oscimp/wr_acorn/26_CERN_Workshop/figures/exp_locksweep_reboots.pdf

WR switch | m2sdr
| phase station

WR link

10 MHz out

auxclk 10 MHz

Microchip 53100A
