oscimp/wr_acorn/26_CERN_Workshop/figures/m2sdr_locksweep_fig.pdf

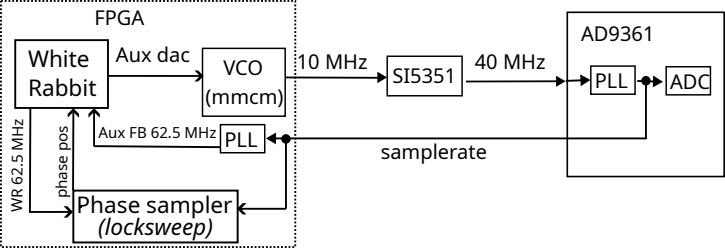
[picture p44: figure]
White Rabbit; Aux dac; VCO; FPGA; PLL; 10 MHz; 40 MHz; ADC; (mmcm); samplerate; Aux FB 62.5 MHz; Phase sampler (locksweep); WR 62.5 MHz; phase pos
