oscimp/wr_acorn/26_CERN_Workshop/figures/m2sdr_syntonized_fig.pdf

White Rabbit; 62.5 MHz; PLL; FPGA; 10 MHz; 40 MHz; ADC
