oscimp/wr_acorn/26_CERN_Workshop/figures/fig_wr_global_view.pdf

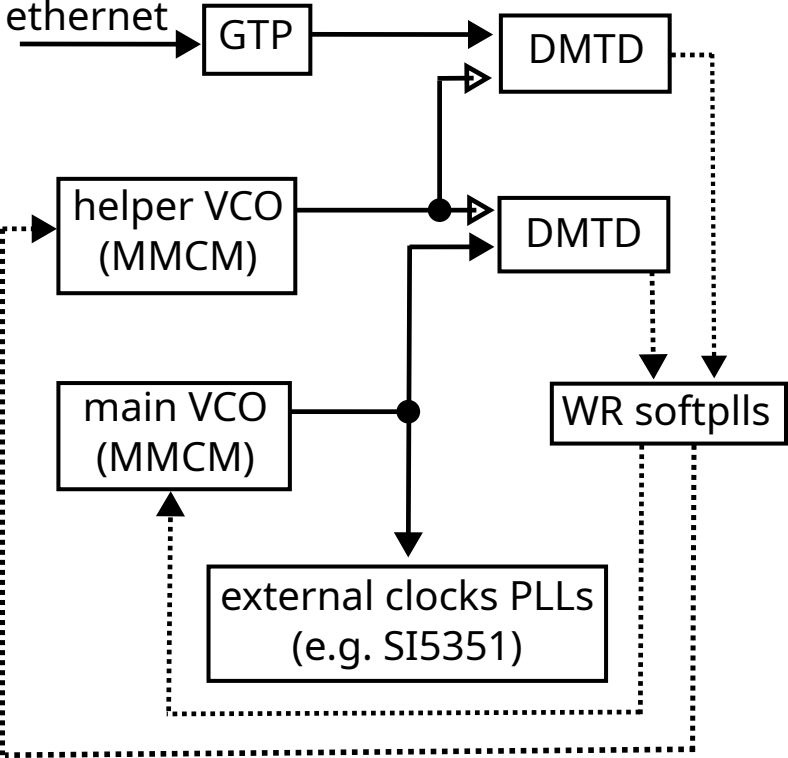
[picture p50: figure]
GTP; DMTD; main VCO (MMCM); helper VCO (MMCM); external clocks PLLs (e.g. SI5351); WR softplls; ethernet
