oscimp/wr_acorn/26_CERN_Workshop/figures/xcorr_principle.pdf

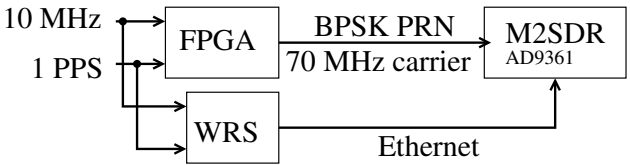
[picture p51: figure]
10 MHz; 1 PPS; FPGA; WRS; Ethernet; BPSK PRN; 70 MHz carrier; M2SDR
