oscimp/wr_acorn/26_CERN_Workshop/figures/ddmtd_schem.pdf

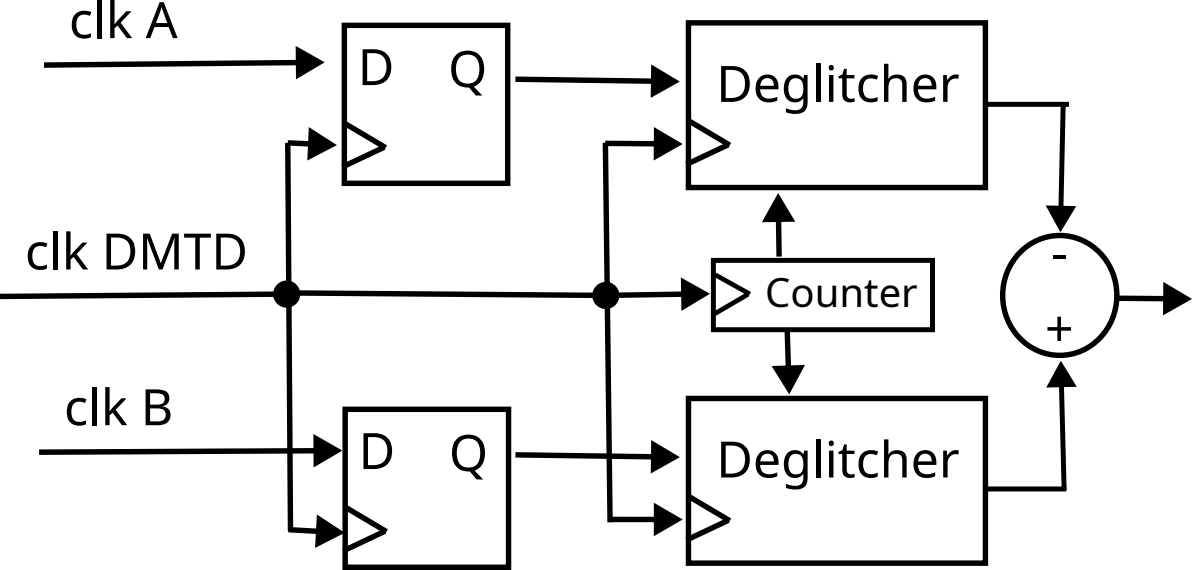
[picture p52: figure]
clk A; clk B; clk DMTD; Deglitcher; - Counter

φ
