oscimp/wr_acorn/26_CERN_Workshop/figures/exp_dmtd_noise_by_beat_freq.pdf

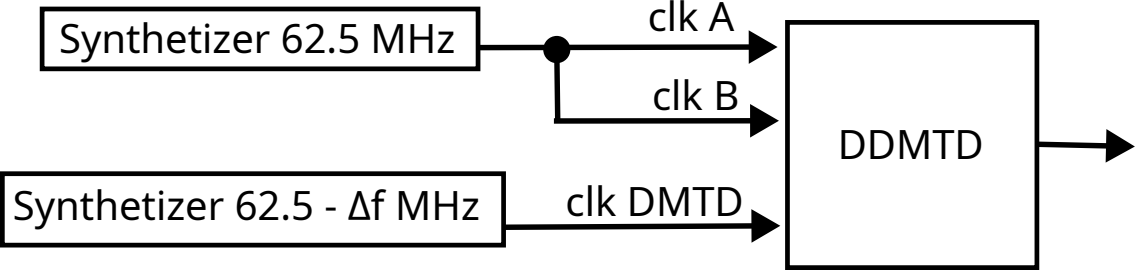
[picture p53: figure]
Synthetizer 62.5 MHz; Synthetizer 62.5 -; Δf MHz; DDMTD; clk A clk B; clk DMTD

P Welch
