oscimp/wr_acorn/26_CERN_Workshop/figures/exp_pll_lock_possibilities.pdf

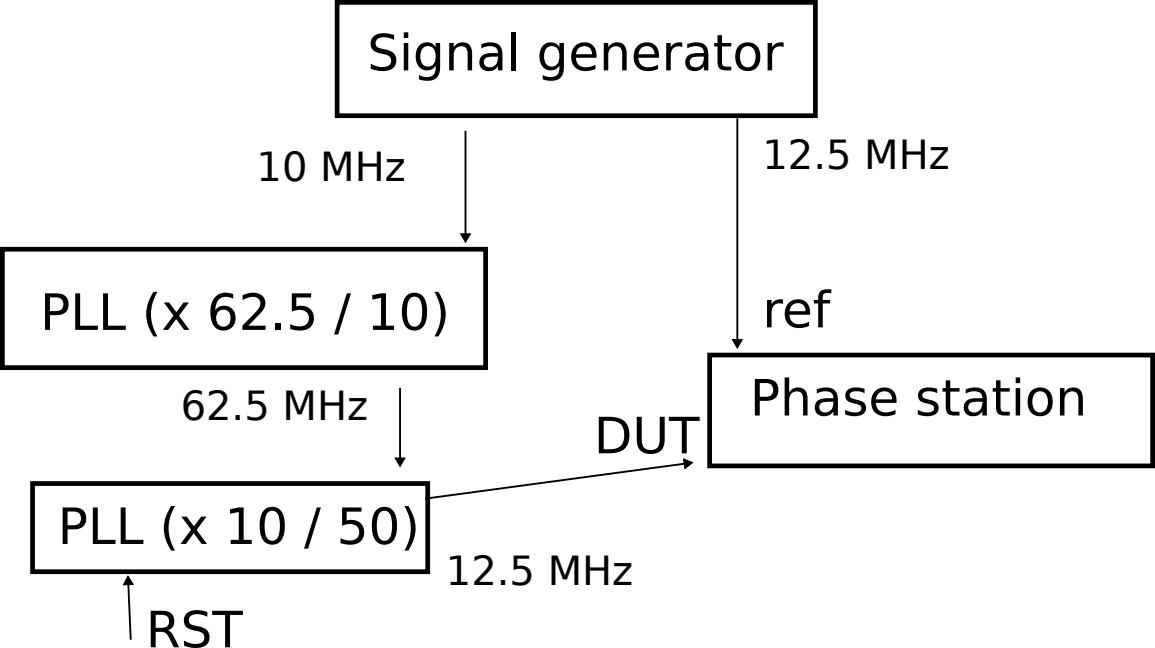
[picture p54: figure]
Phase station; PLL (x 10 / 50); PLL (x 62.5 / 10); Signal generator; 10 MHz; 12.5 MHz; 62.5 MHz; ref; DUT; RST
