oscimp/wr_acorn/26_CERN_Workshop/figures/ad9361_locksweep.pdf

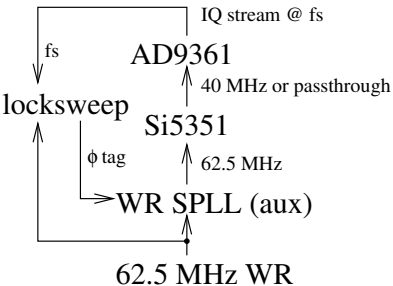
[picture p55: figure]
40 MHz or passthrough; 62.5 MHz WR; 62.5 MHz WR SPLL (aux); locksweep; φ tag; IQ stream @ fs
