oscimp/wr_acorn/26_CERN_Workshop/figures/locksweep_comparison.pdf

## Before aux locksweep

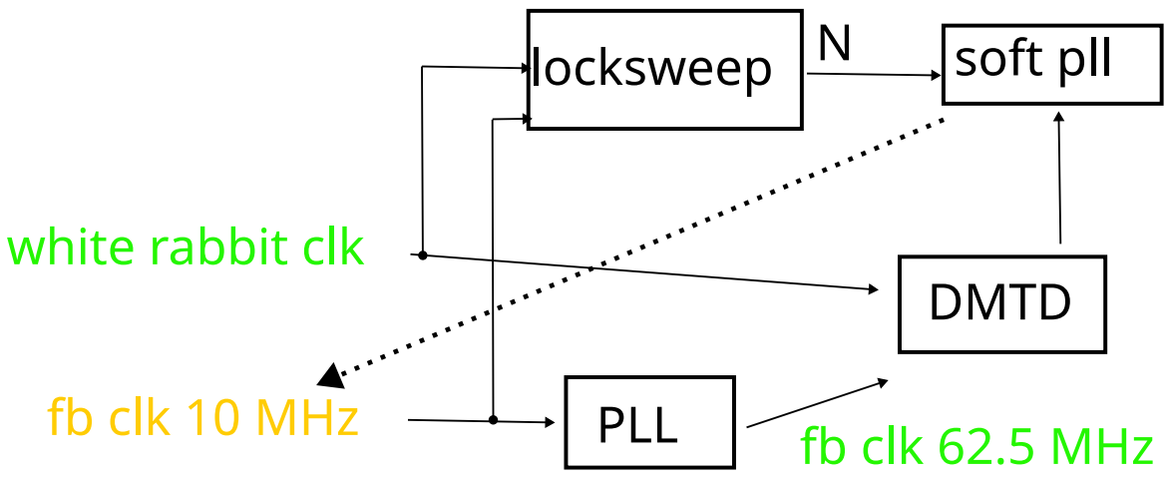
[picture p56: figure]
fb clk 10 MHz; PLL; locksweep; white rabbit clk; DMTD; soft pll; fb clk 62.5 MHz

## After aux locksweep

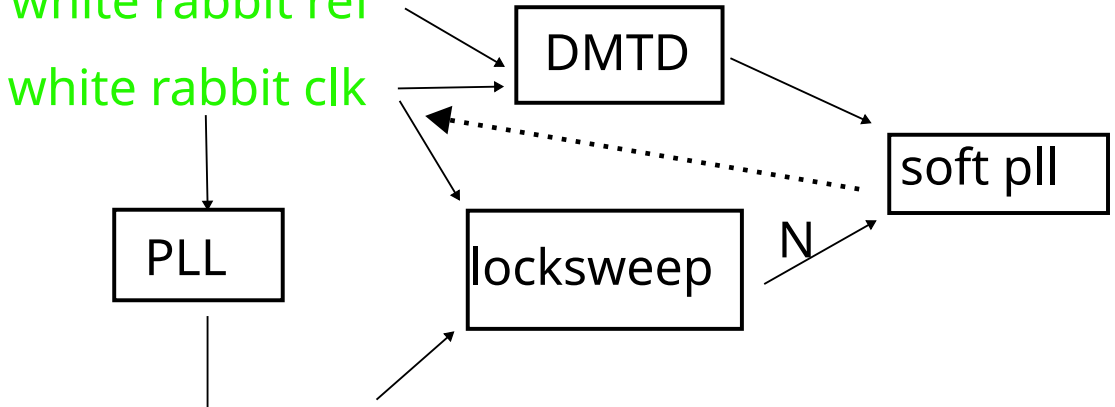
[picture p57: figure]
PLL; locksweep; white rabbit clk; DMTD; soft pll

## white rabbit 10 MHz

## white rabbit ref

## Before locksweep

delock and swipe white rabbit clk by N periods

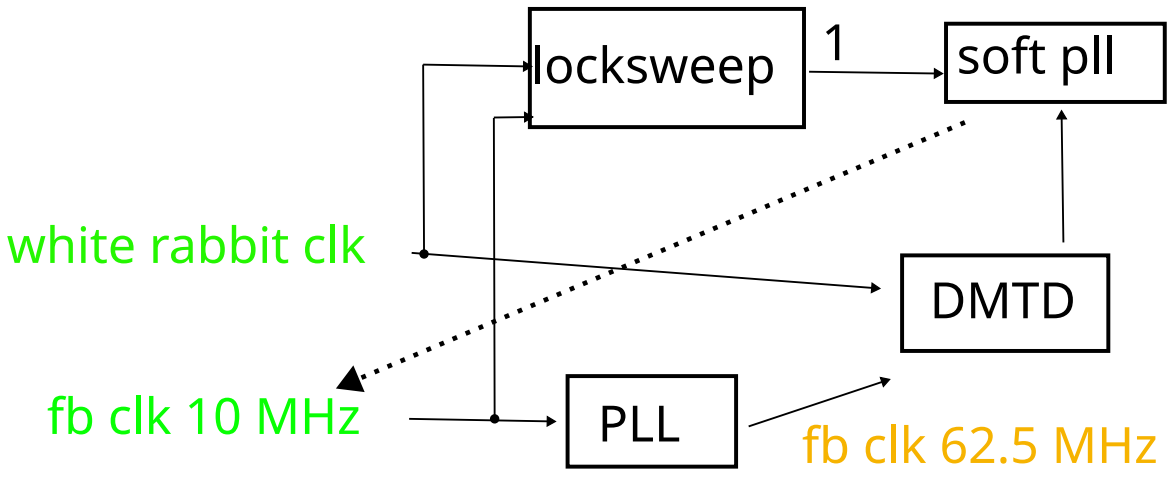
[picture p58: figure]
fb clk 10 MHz; PLL; locksweep; white rabbit clk; DMTD; soft pll; fb clk 62.5 MHz
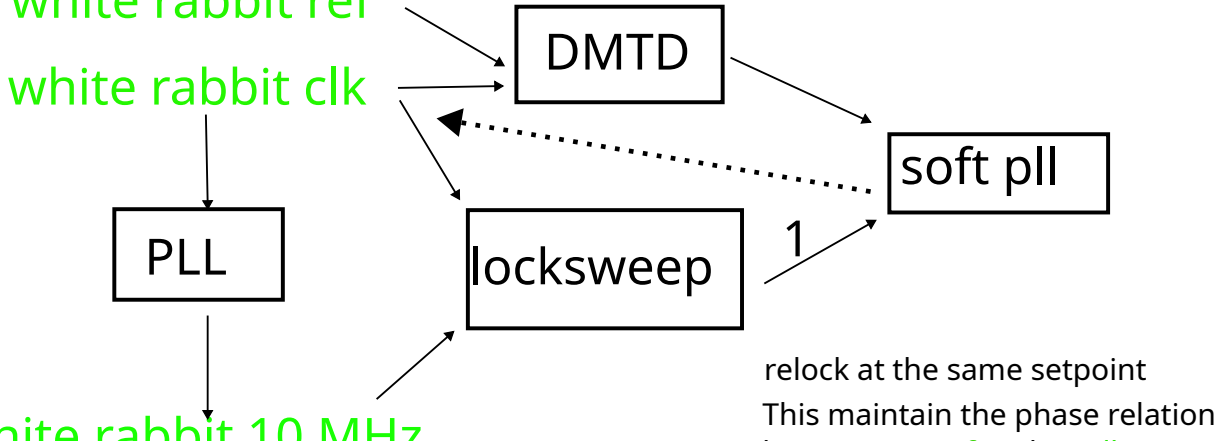
[picture p59: figure]
PLL; locksweep; white rabbit clk; DMTD; soft pll; relock at the same setpoint This maintain the phase relation

## white rabbit 10 MHz

## white rabbit ref

## After locksweep

equivalent to modifying the setpoint by setpoint += (N-1) * 16 ns

## Syntonised and determinist in phase

## Syntonised but not determinist in phase

between wr ref and wr clk

Phase shift fb clk 62.5 MHz by
setpoint += ((N-1) * 16 ns) % 100 ns
In practice our locksweep LUT outputs another number :
M = (N * 16 / GCD(16, 100) % N_phi , this avoid the modulo in the software : setpoint += (M-1) * GCD(16, 100)

fb clk 62.5 MHz is not deterministic but it shouldn't matter since it is only used for the DMTD
