oscimp/wr_acorn/25_CERN_Workshop/figures/band-width.png

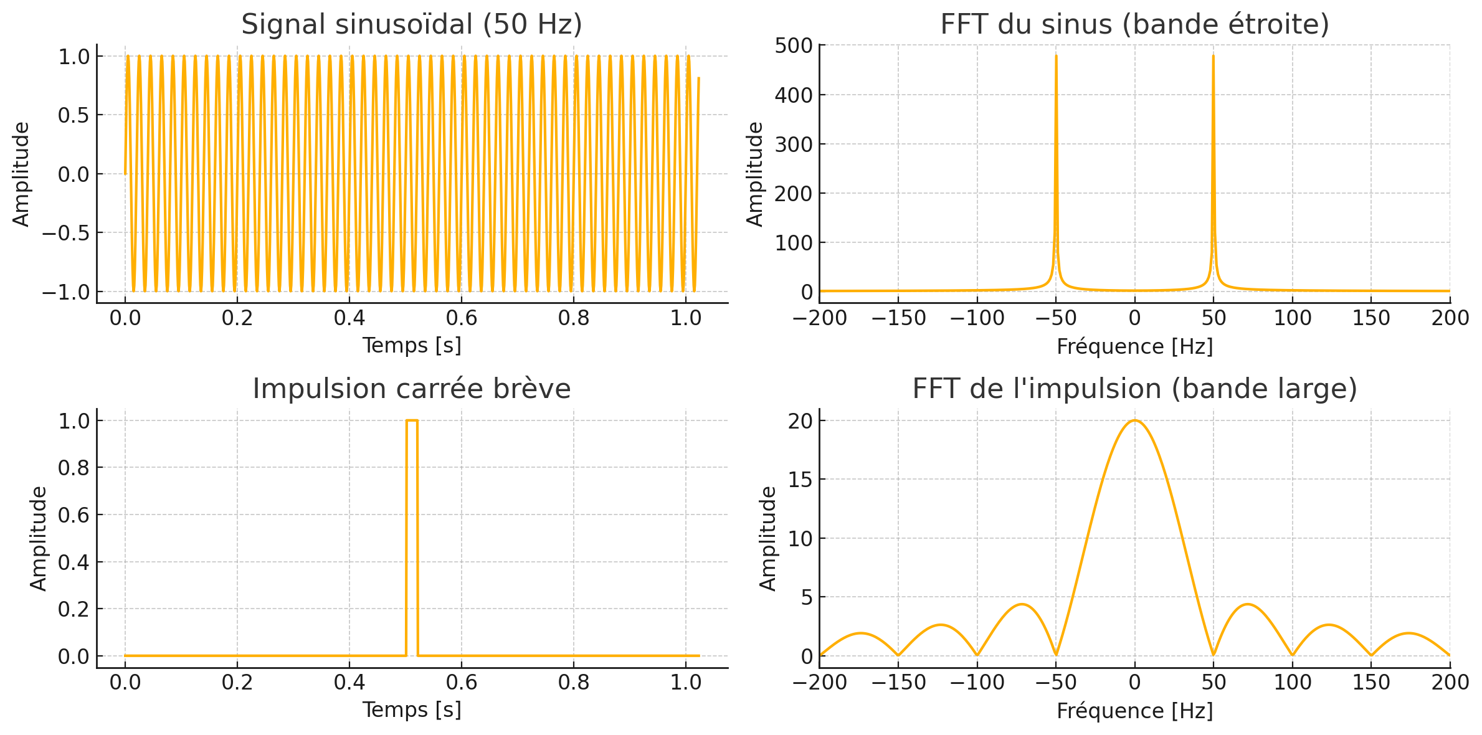
25_CERN_Workshop/figures/band-width.png
