oscimp/wr_acorn/25_CERN_Workshop/figures/pps_sync.png

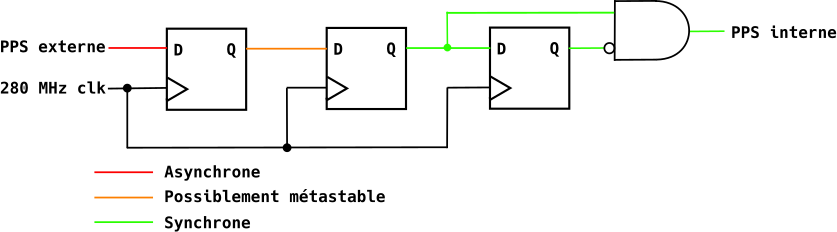
25_CERN_Workshop/figures/pps_sync.png
