oscimp/wr_acorn/25_CERN_Workshop/figures/ptp.png

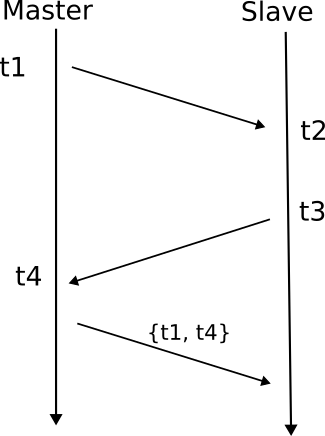
25_CERN_Workshop/figures/ptp.png
