oscimp/wr_acorn/26_CERN_Workshop/figures/fft.png

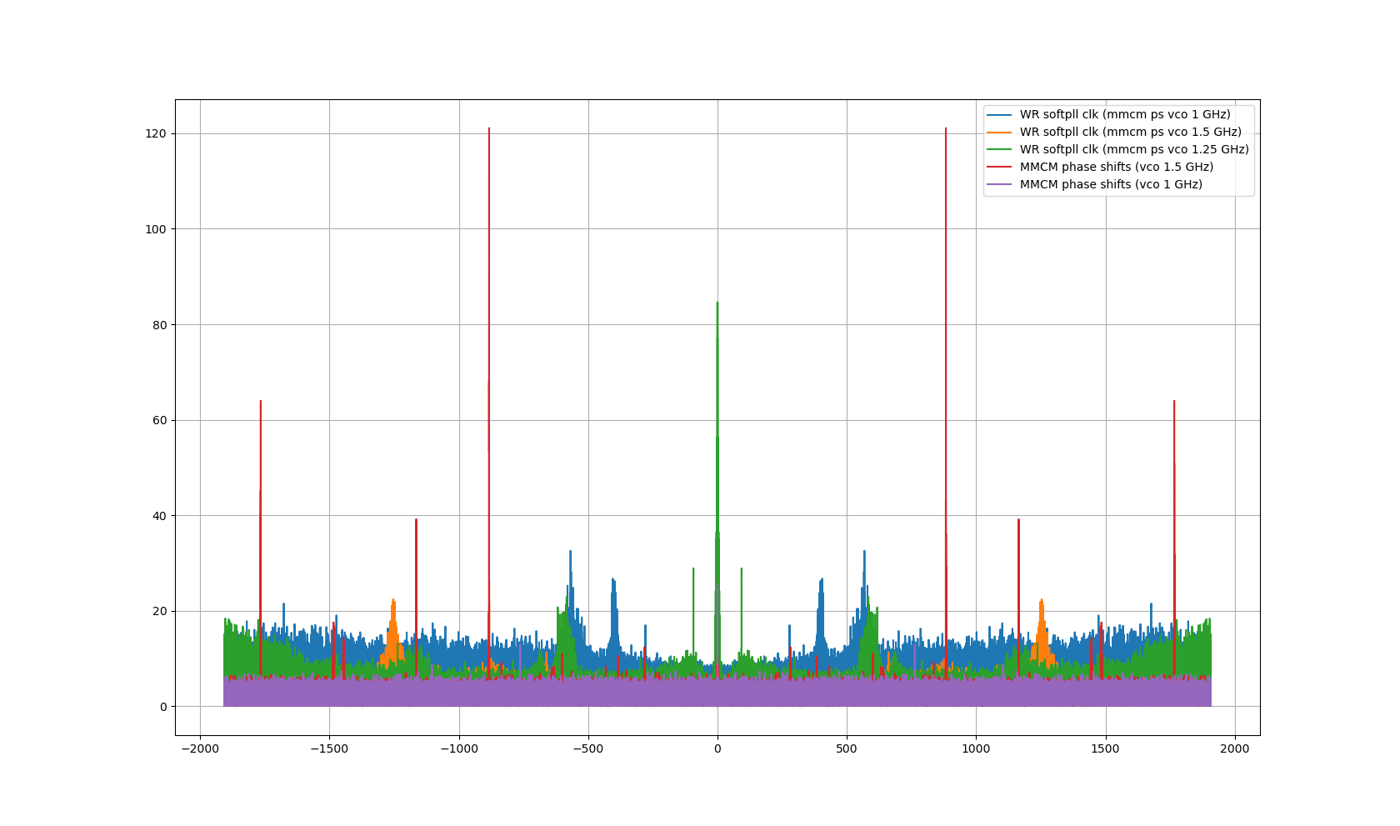
26_CERN_Workshop/figures/fft.png
