oscimp/wr_acorn/26_CERN_Workshop/figures/freq_by_spur_100k108k.png

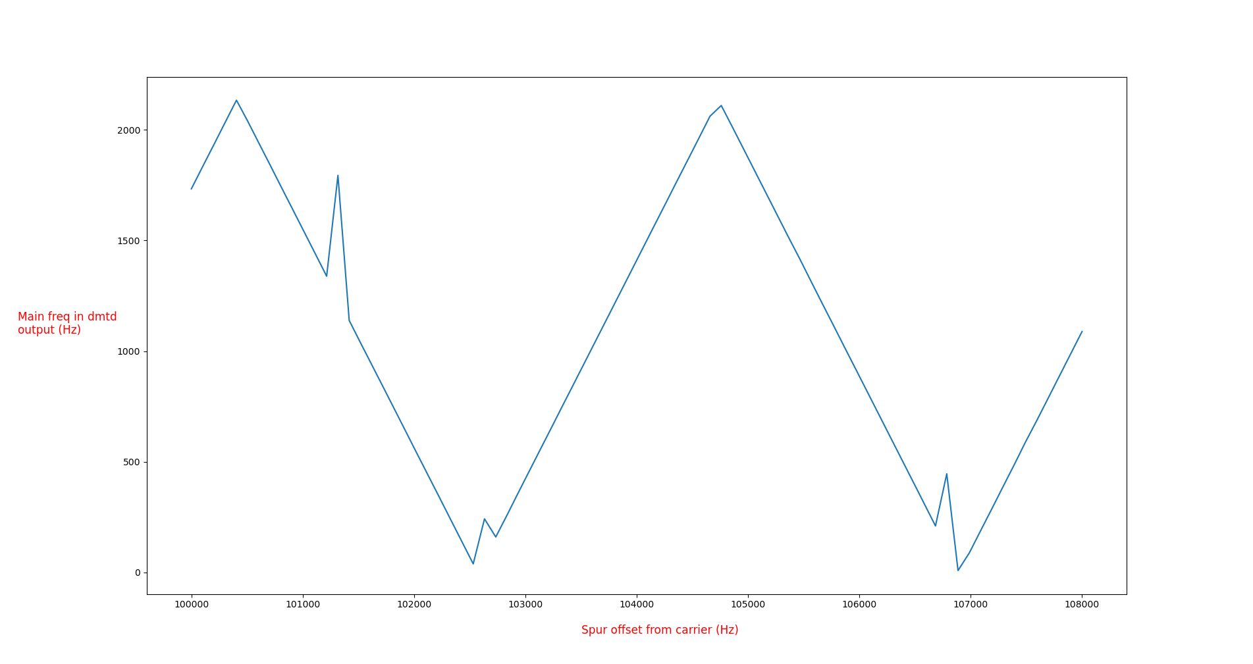
26_CERN_Workshop/figures/freq_by_spur_100k108k.png
