oscimp/wr_acorn/26_CERN_Workshop/figures/phase_diff_synth.png

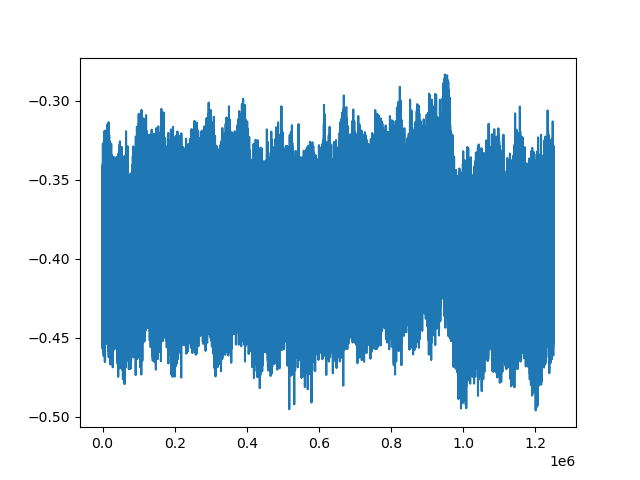
26_CERN_Workshop/figures/phase_diff_synth.png
