oscimp/wr_acorn/26_CERN_Workshop/figures/wr_alternative_clocking_comparison.png

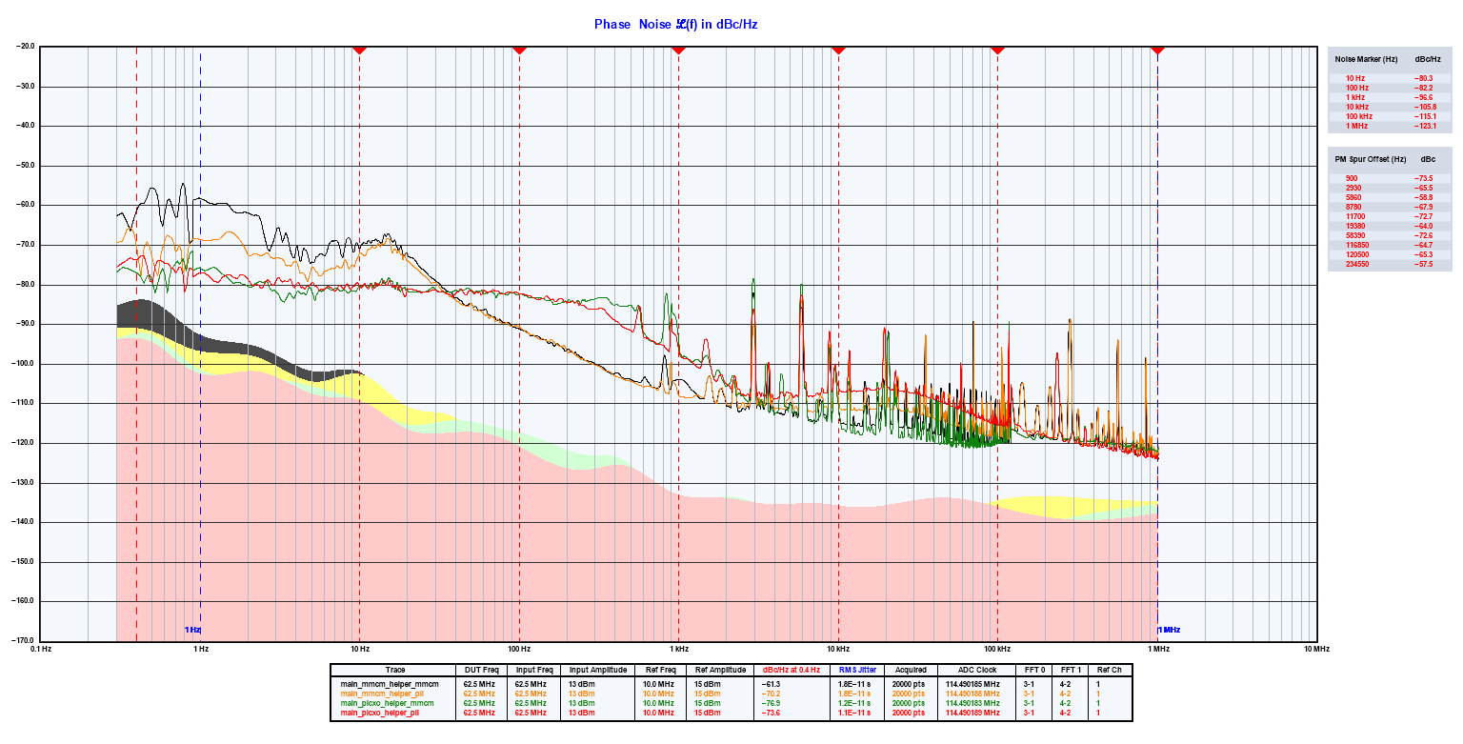
26_CERN_Workshop/figures/wr_alternative_clocking_comparison.png
