oscimp/wr_acorn/251018_screenshots/2025-10-18-162801_3360x1050_scrot.png

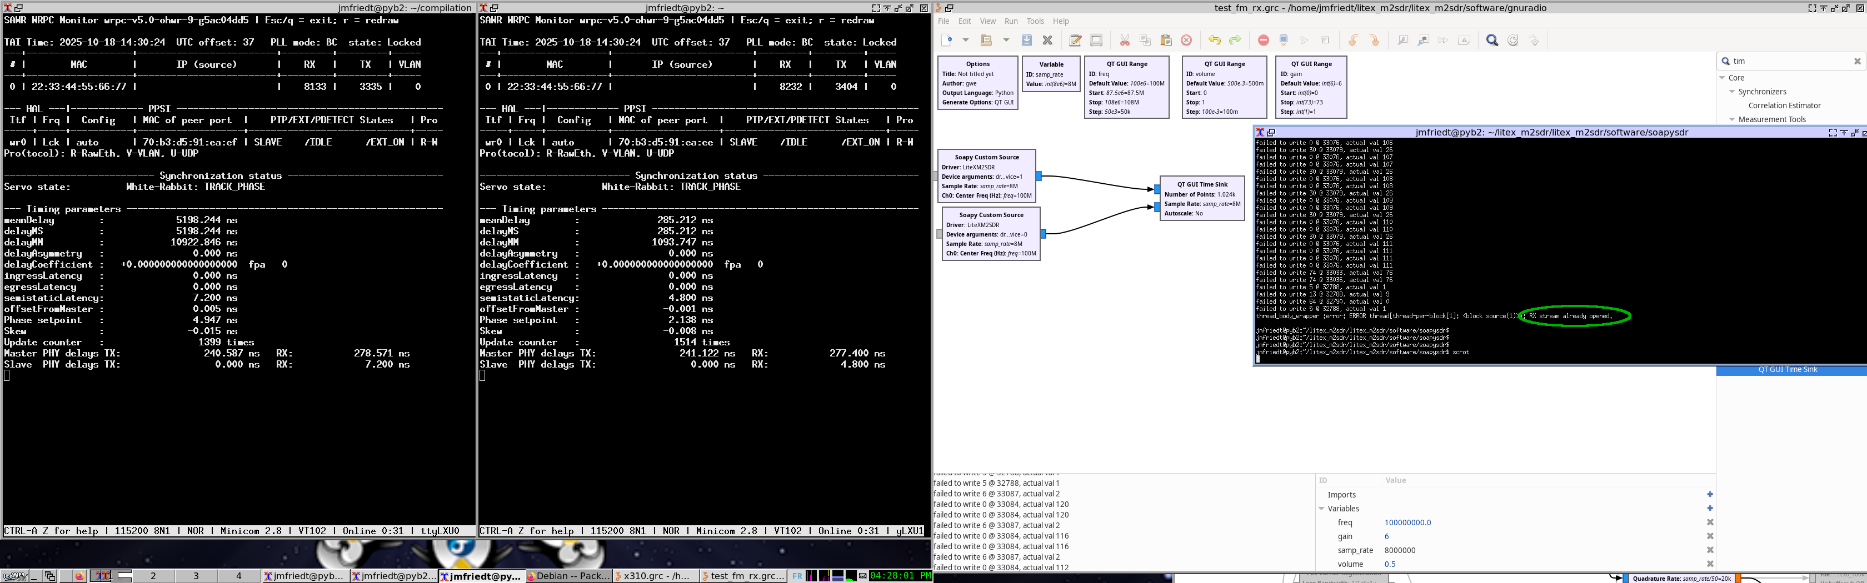
251018_screenshots/2025-10-18-162801_3360x1050_scrot.png
