oscimp/wr_acorn/dual_M2SDR_phase_unlocked.png

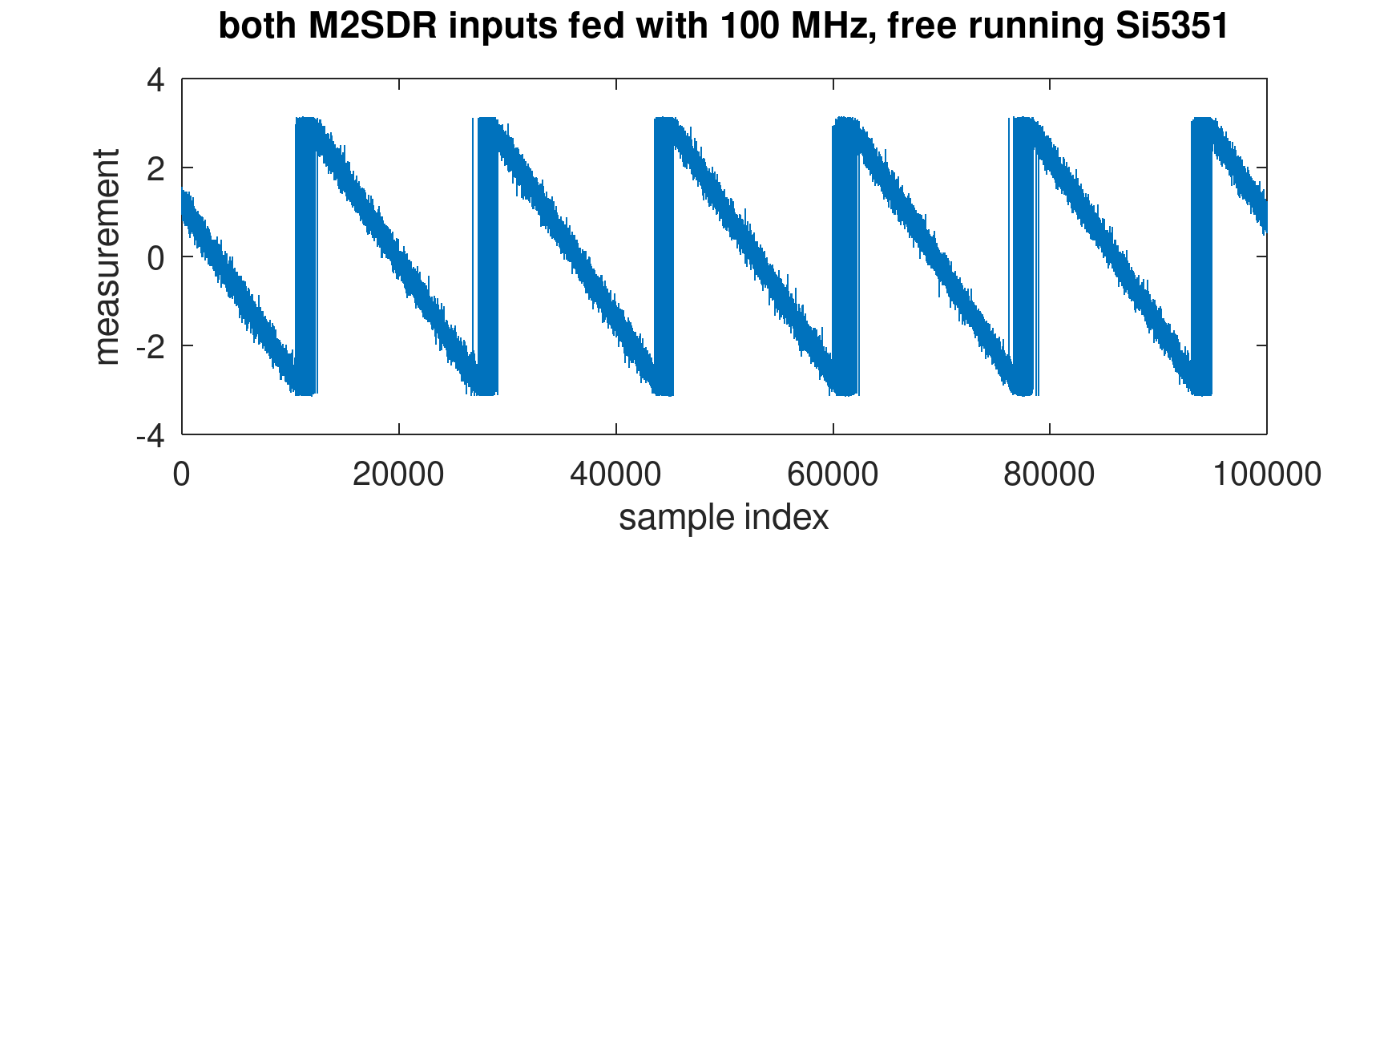
dual_M2SDR_phase_unlocked.png
