oscimp/wr_acorn/phase_shift_mmcm/figures/nonlinearities_comp_simulation.png

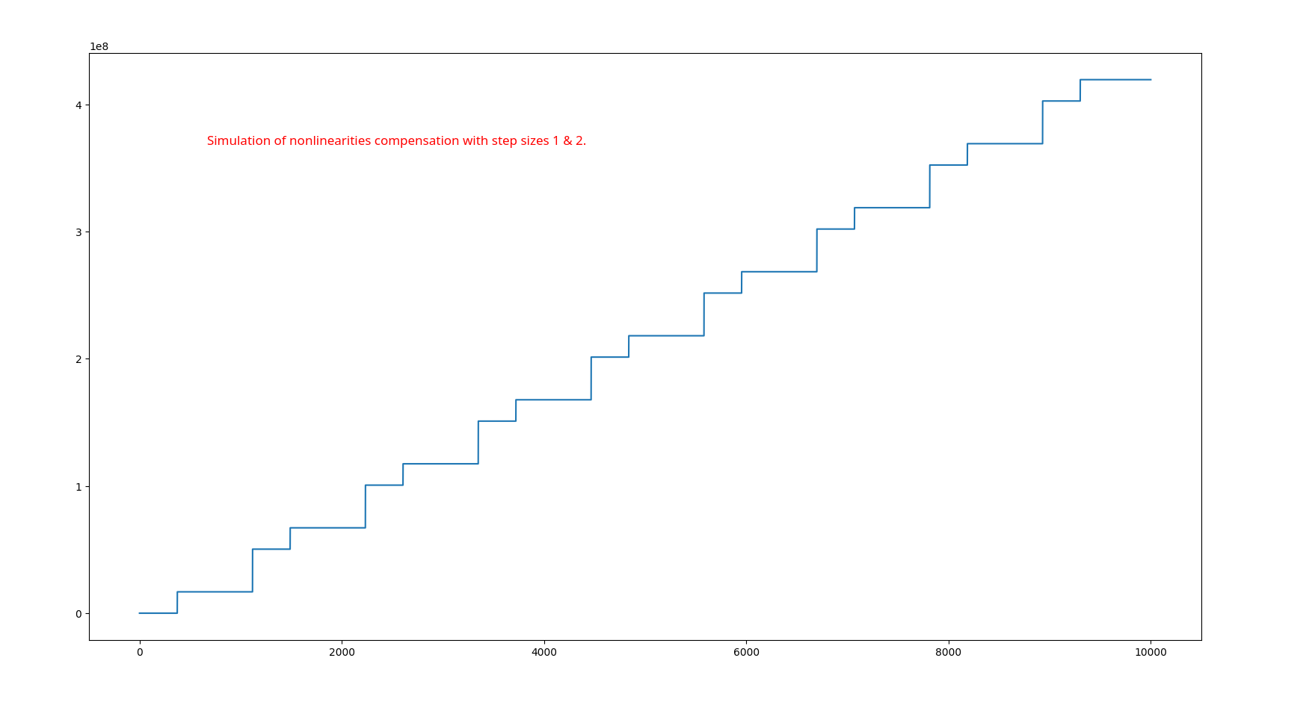
phase_shift_mmcm/figures/nonlinearities_comp_simulation.png
