oscimp/wr_acorn/RPi_HAT/rpi5_m2sdr.png

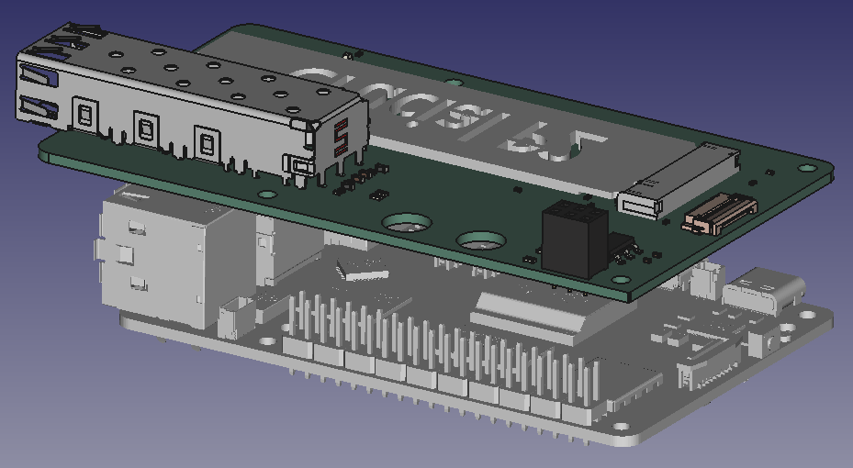
RPi_HAT/rpi5_m2sdr.png
