oscimp/wr_acorn/26_CERN_Workshop/figures/plt_temperature_drift.pdf

49

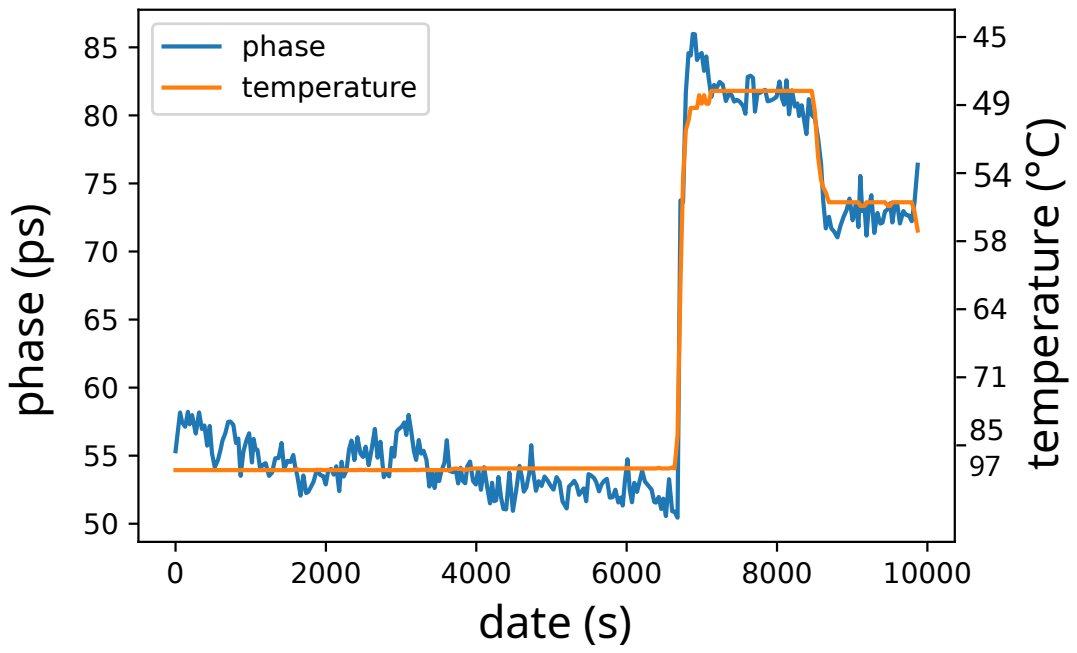
[picture p78: page 1]
phase temperature; phase (ps); temperature (°C); date (s)
