oscimp/wr_acorn/26_CERN_Workshop/figures/FSFE_Public_Money,_Public_Code_logo_sticker.pdf

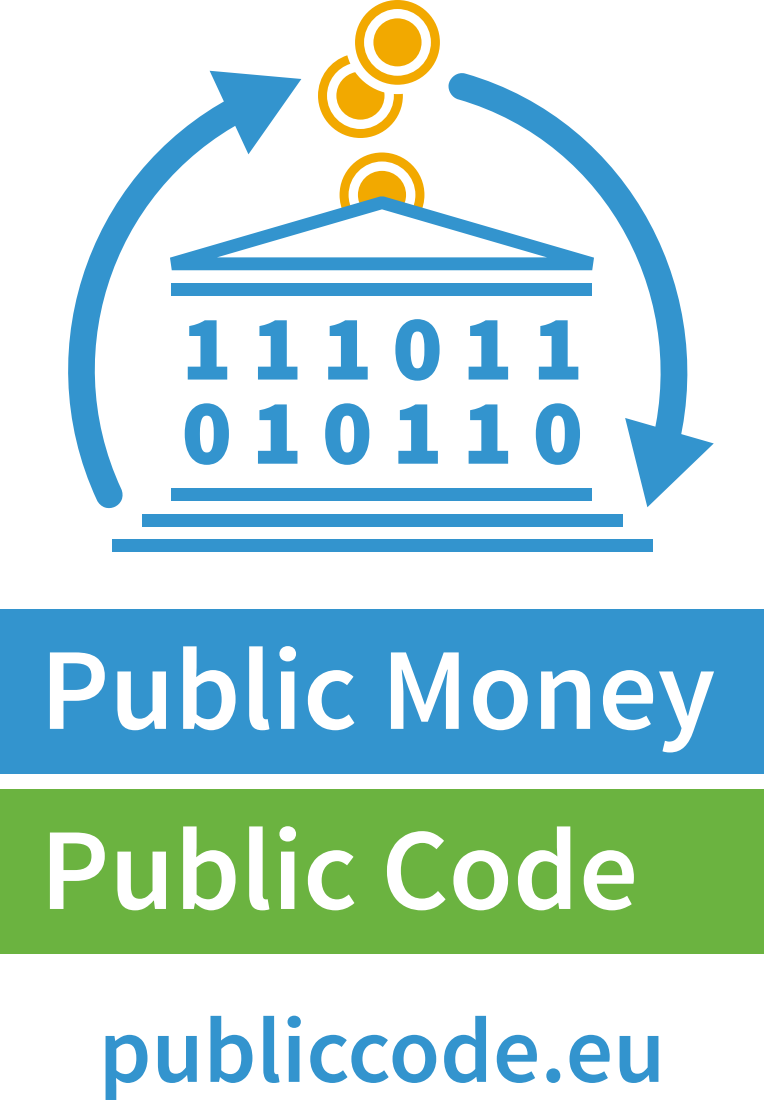
[picture p84: page 1]
