oscimp/wr_acorn/26_CERN_Workshop/figures/dmtd_noise_nonlinear_freq_depth.pdf

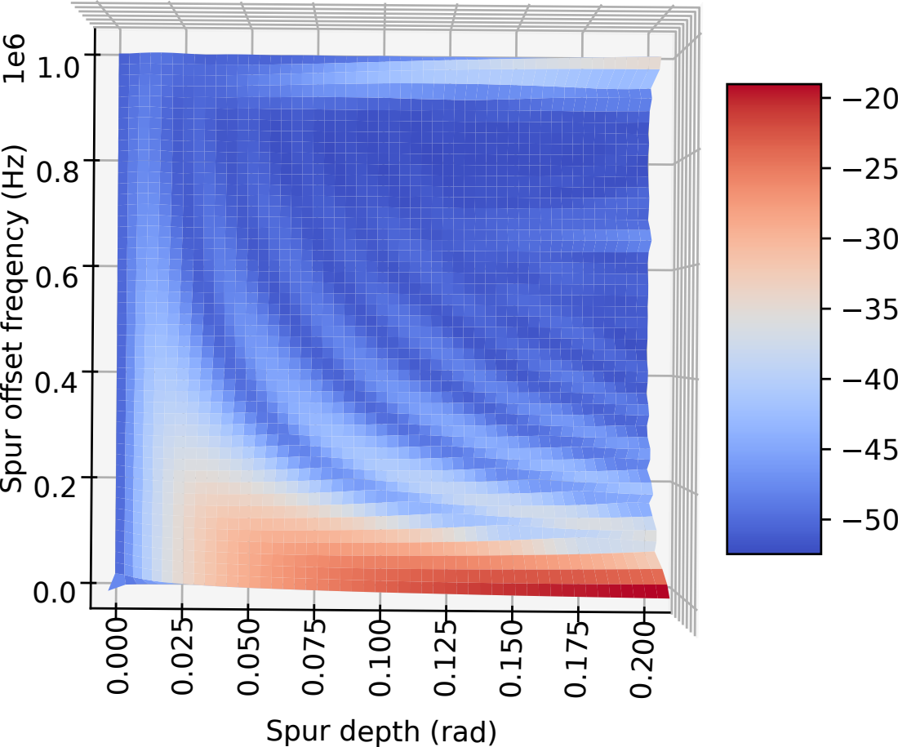
[picture p85: page 1]

1e6 1.0 Spur offset freqency (Hz)

Spur depth (rad)
