oscimp/wr_acorn/26_CERN_Workshop/figures/ddmtd_noise_by_beat_freq_1k_2k.pdf

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

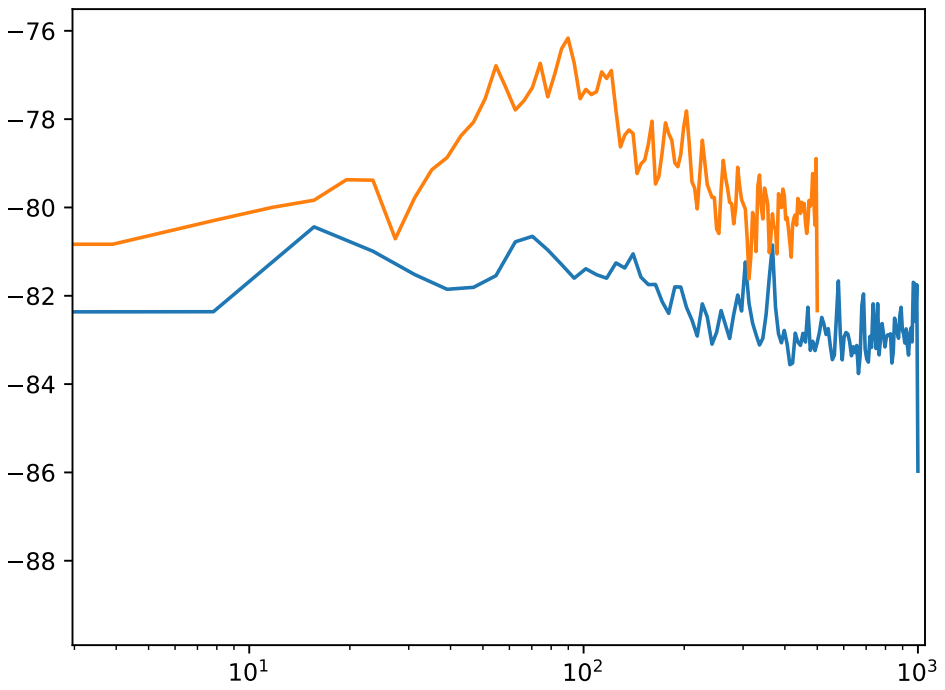
[picture p87: page 1]
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
