oscimp/wr_acorn/26_CERN_Workshop/figures/plt_phase_station_indeterminism_zoom.pdf

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

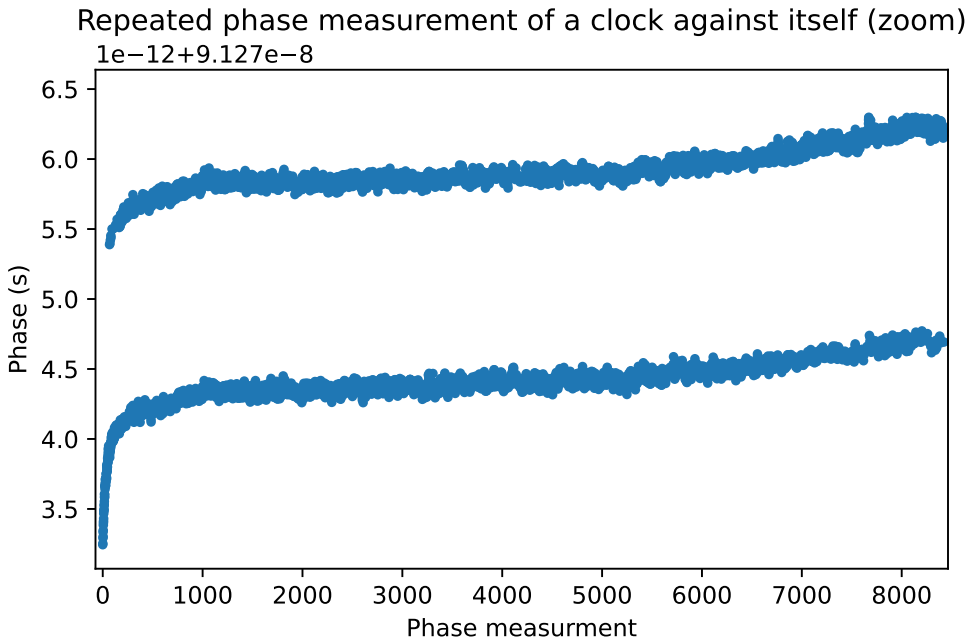
[picture p89: page 1]
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
