oscimp/wr_acorn/26_CERN_Workshop/figures/plt_pll_lock_possibilities_zoom.pdf

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

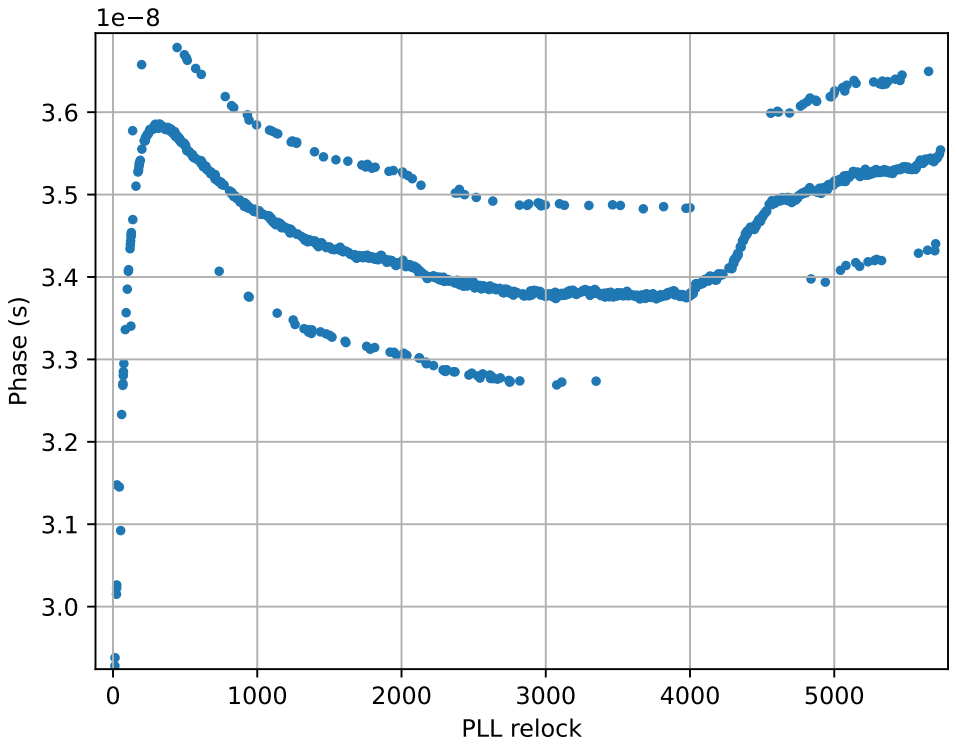
[picture p91: page 1]
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
