oscimp/wr_acorn/25_CERN_Workshop/figures/phase_noise.pdf

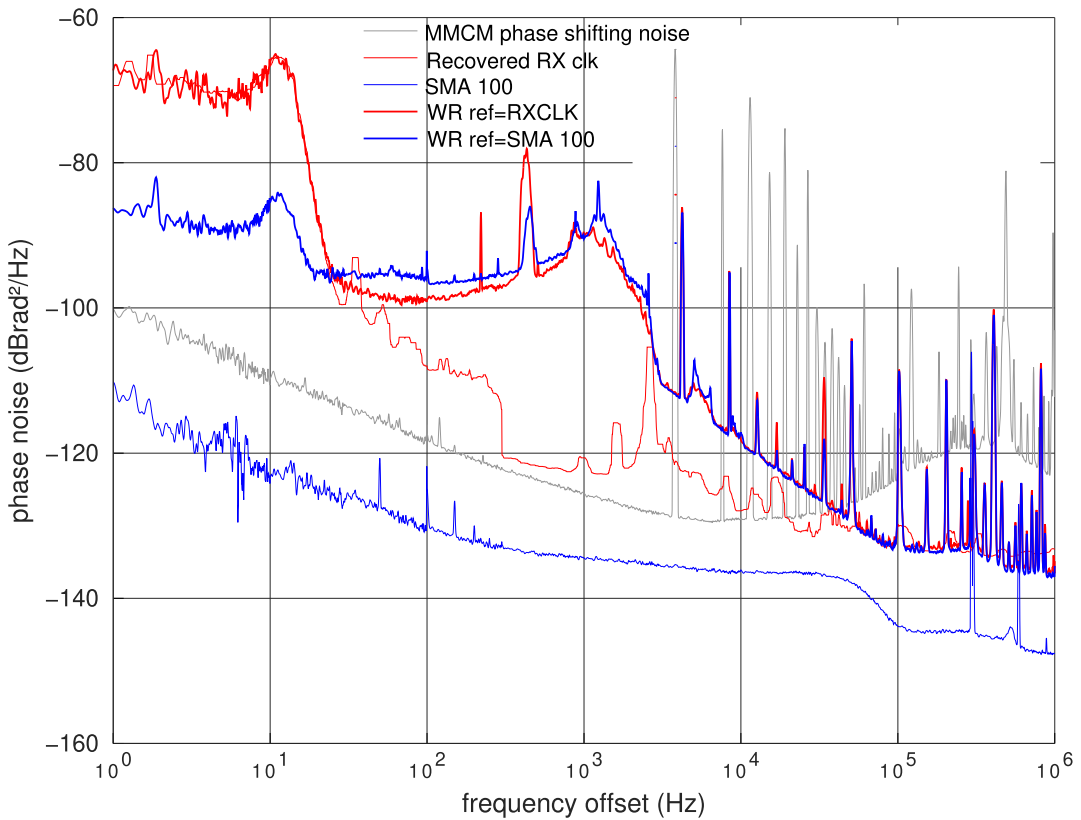
[picture p92: page 1]
