oscimp/wr_acorn/25_CERN_Workshop/figures/dmtd_phase_noise_by_clk_src.pdf

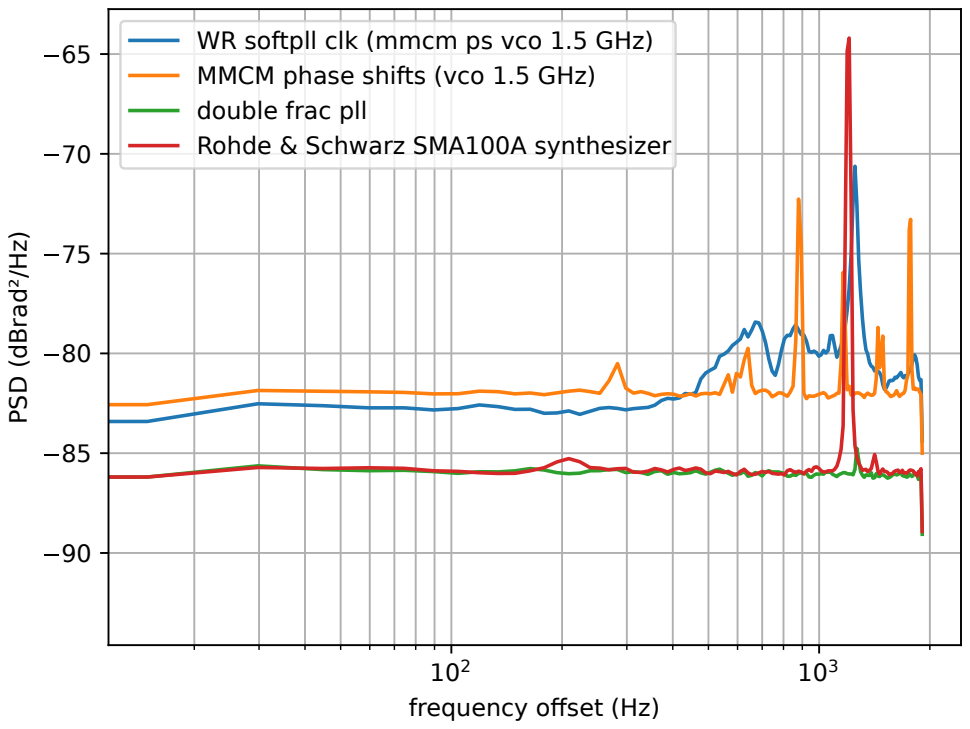
[picture p93: page 1]

WR softpll clk (mmcm ps vco 1.5 GHz)
MMCM phase shifts (vco 1.5 GHz) double frac pll Rohde & Schwarz SMA100A synthesizer

PSD (dBrad²/Hz)

frequency offset (Hz)
