oscimp/wr_acorn/25_CERN_Workshop/figures/mmcm_phase_noise.pdf

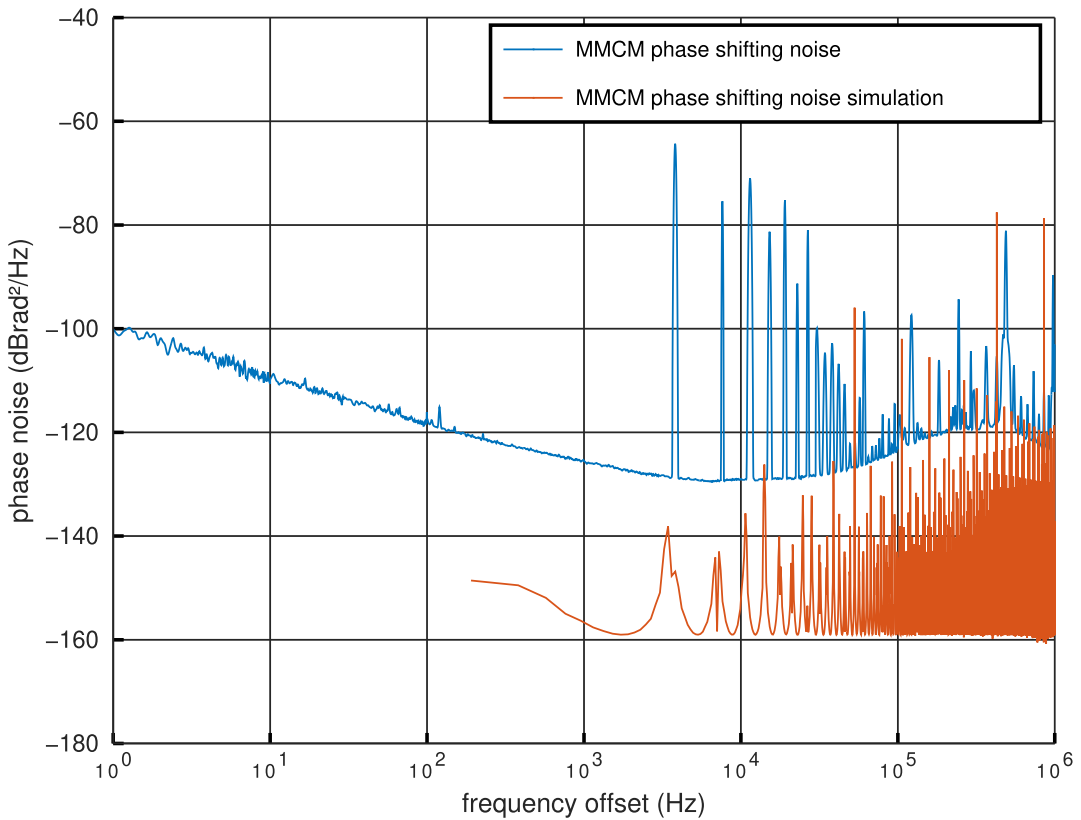
[picture p94: page 1]
