oscimp/wr_acorn/25_CERN_Workshop/figures/phase_noise_litex.pdf

-200

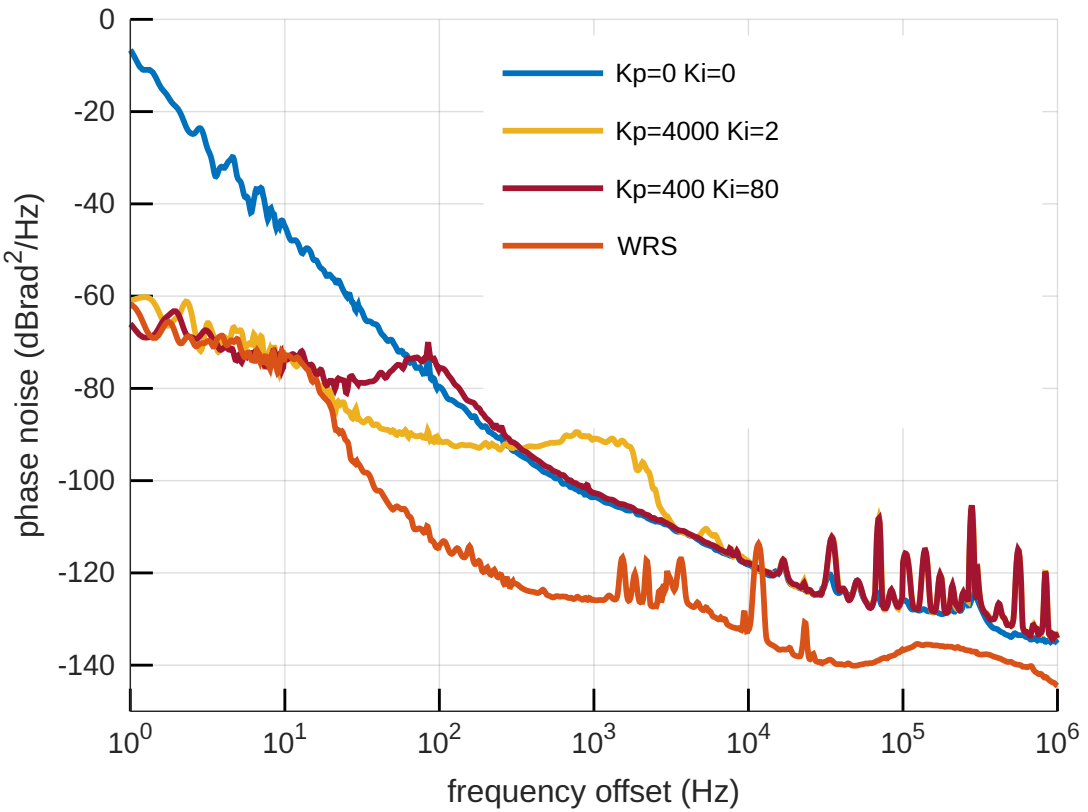
[picture p95: page 1]

phase noise (dBrad2/Hz)

WRS

frequency offset (Hz)
