oscimp/wr_acorn/25_CERN_Workshop/figures/allan_wr_acorn_new.pdf

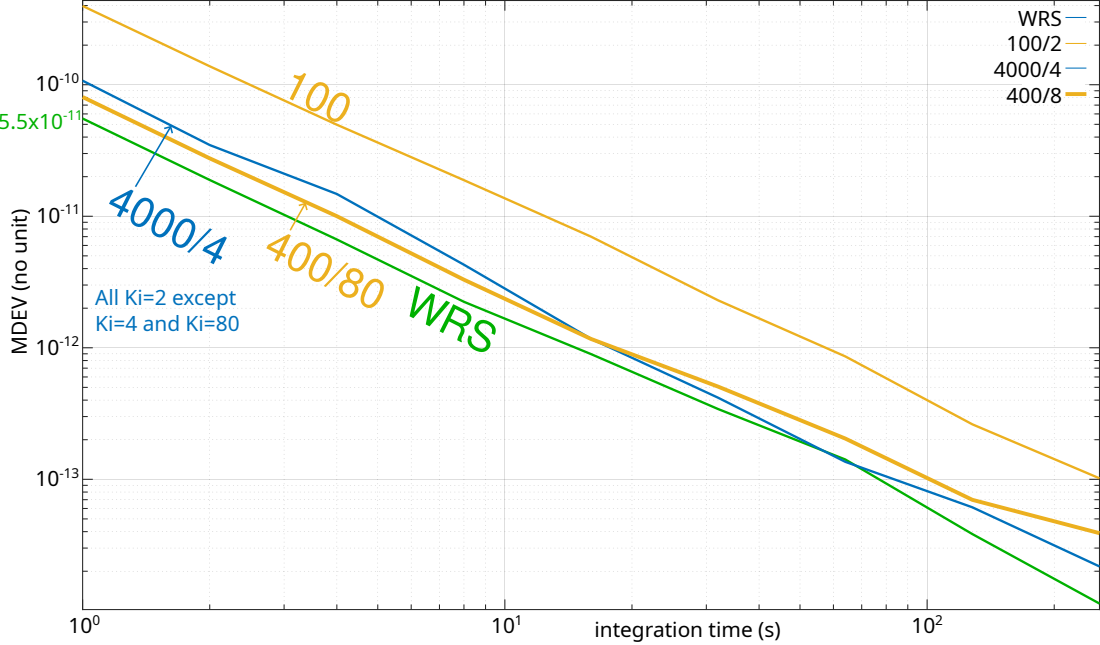
[picture p96: page 1]
WRS 400/80; integration time (s)

WRS 100/2 4000/4

MDEV (no unit)

All Ki=2 except Ki=4 and Ki=80
