oscimp/wr_acorn/25_CERN_Workshop/figures/freerunning_pps.Mdev.pdf

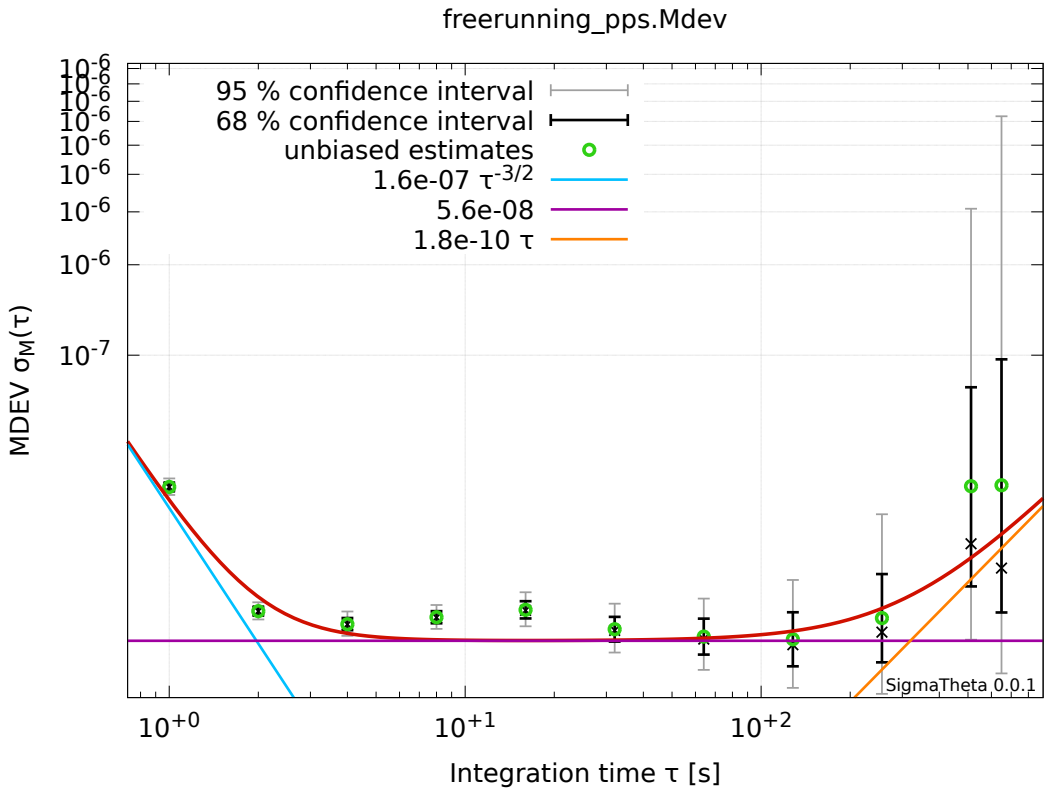
[picture p97: page 1]
SigmaTheta 0.0.1; 95 % confidence interval 68 % confidence interval unbiased estimates 1.6e-07 τ⁻³/2 5.6e-08 1.8e-10 τ; MDEV; Integration time τ [s]; freerunning_pps.Mdev
