oscimp/wr_acorn/25_CERN_Workshop/figures/freerunning_pps2.Mdev.pdf

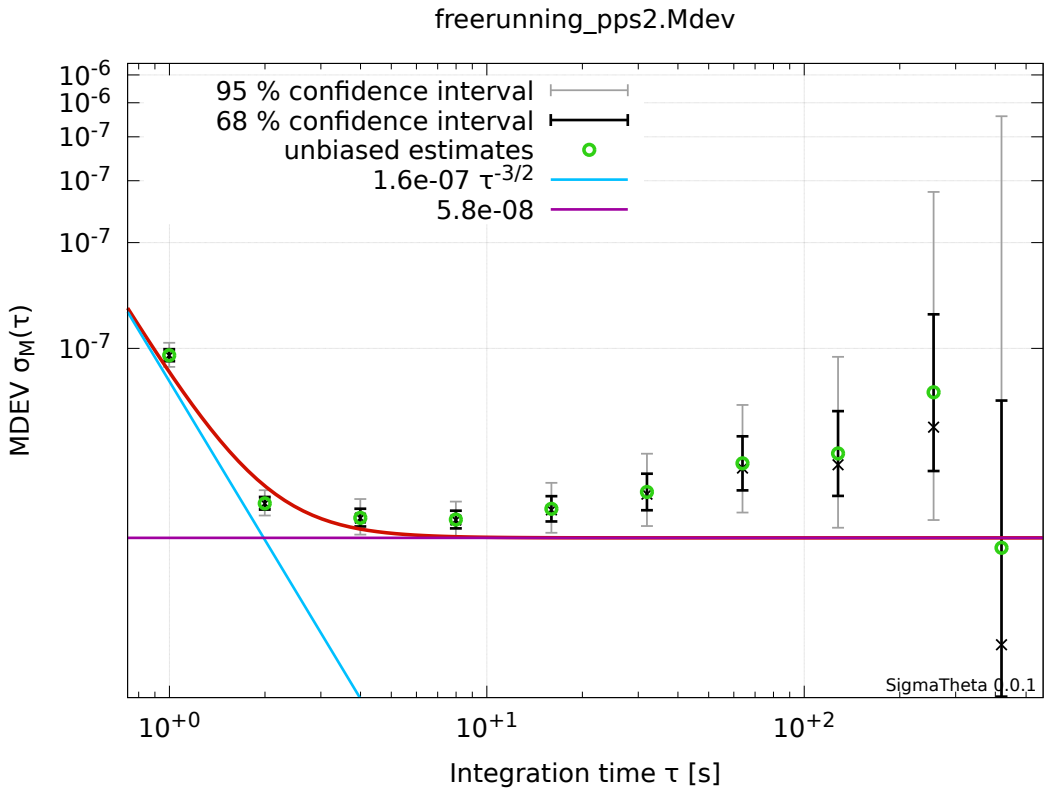
[picture p98: page 1]
SigmaTheta 0.0.1; 95 % confidence interval 68 % confidence interval unbiased estimates 1.6e-07 τ⁻³/2 5.8e-08; MDEV; Integration time τ [s]; freerunning_pps2.Mdev
