oscimp/wr_acorn/25_CERN_Workshop/figures/freerunning_pps_m2sdr.adev.pdf

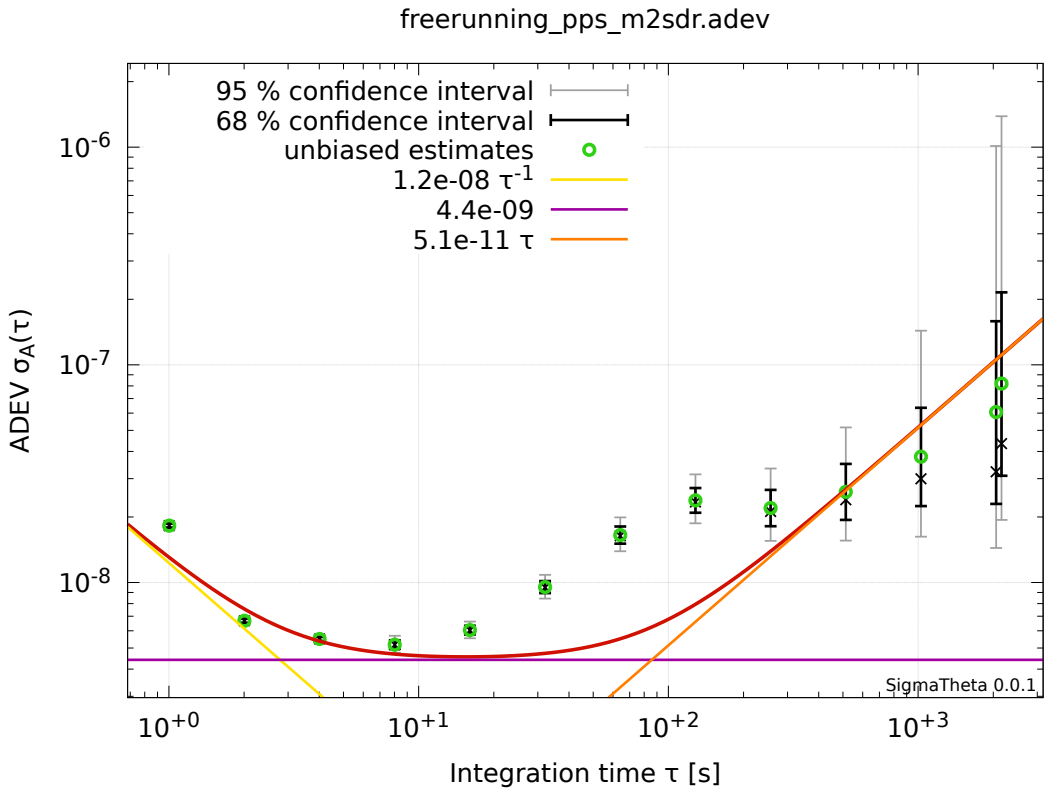
[picture p99: page 1]
SigmaTheta 0.0.1; 95 % confidence interval 68 % confidence interval unbiased estimates 1.2e-08 τ⁻¹ 4.4e-09 5.1e-11 τ; ADEV; Integration time τ [s]; freerunning_pps_m2sdr.adev
