oscimp/wr_acorn/25_CERN_Workshop/figures/freerunning_pps_m2sdr.Mdev.pdf

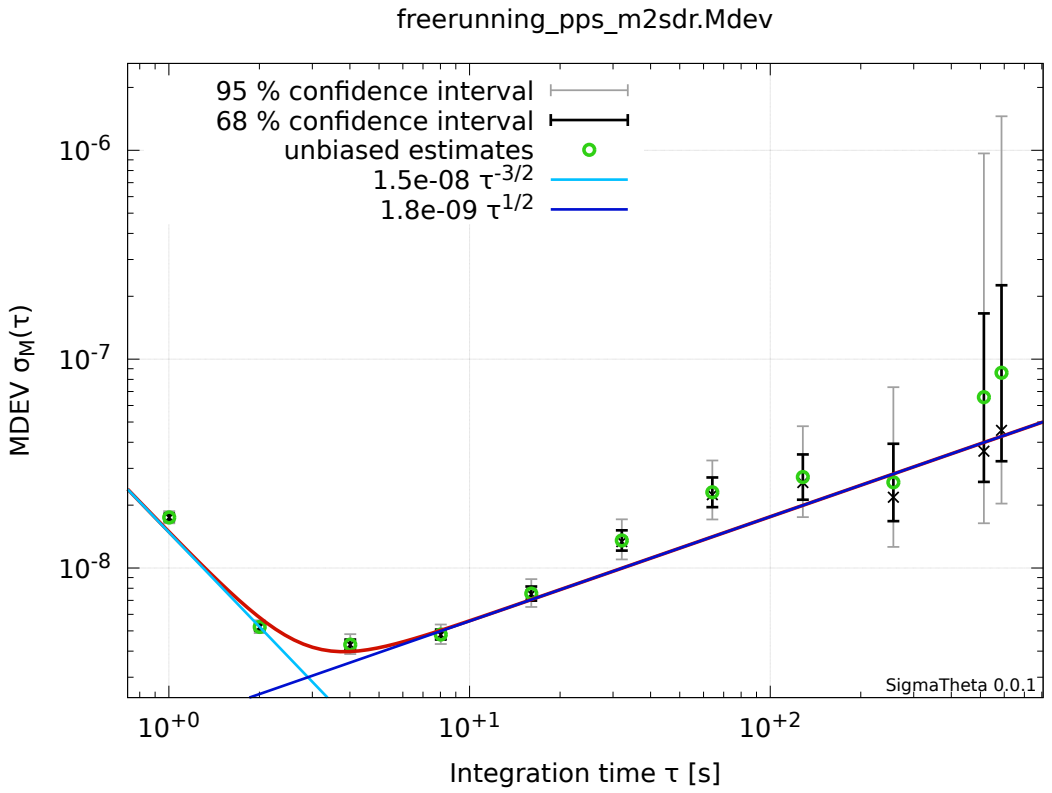
[picture p100: page 1]
SigmaTheta 0.0.1; 95 % confidence interval 68 % confidence interval unbiased estimates 1.5e-08 τ⁻³/2 1.8e-09 τ¹/2; MDEV; Integration time τ [s]; freerunning_pps_m2sdr.Mdev
