oscimp/wr_acorn/25_CERN_Workshop/figures/62p5MHz.pdf

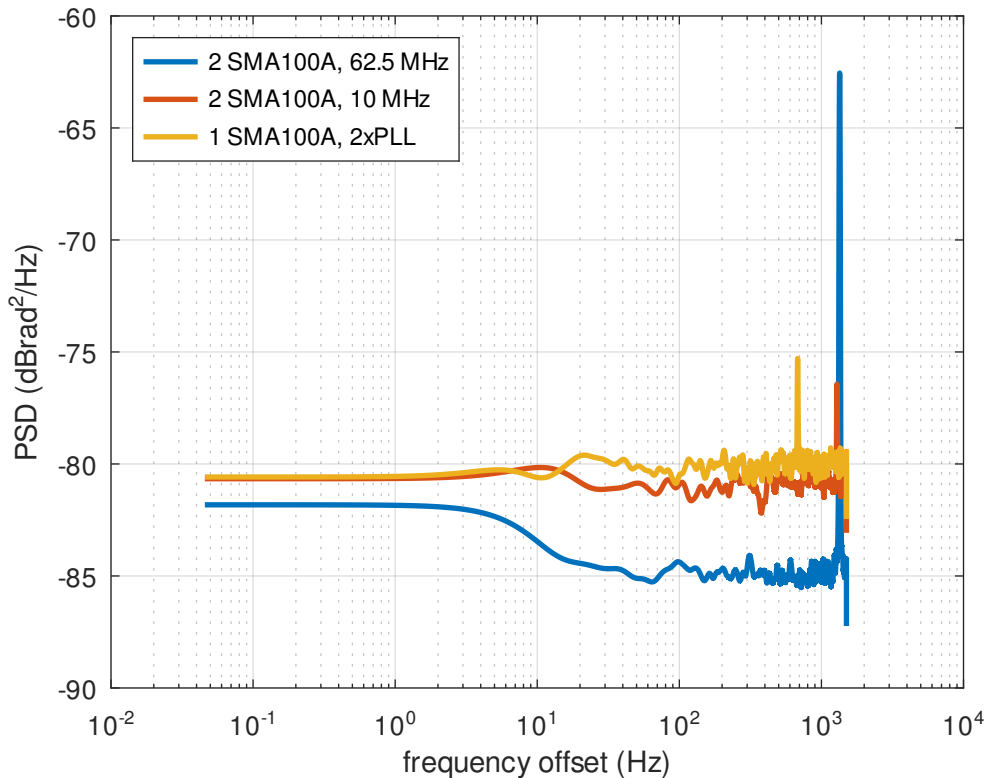
[picture p101: page 1]
PSD (dBrad2/Hz)

2 SMA100A, 62.5 MHz 2 SMA100A, 10 MHz

1 SMA100A, 2xPLL

frequency offset (Hz)
