oscimp/wr_acorn/25_CERN_Workshop/figures/m2sdr.pdf

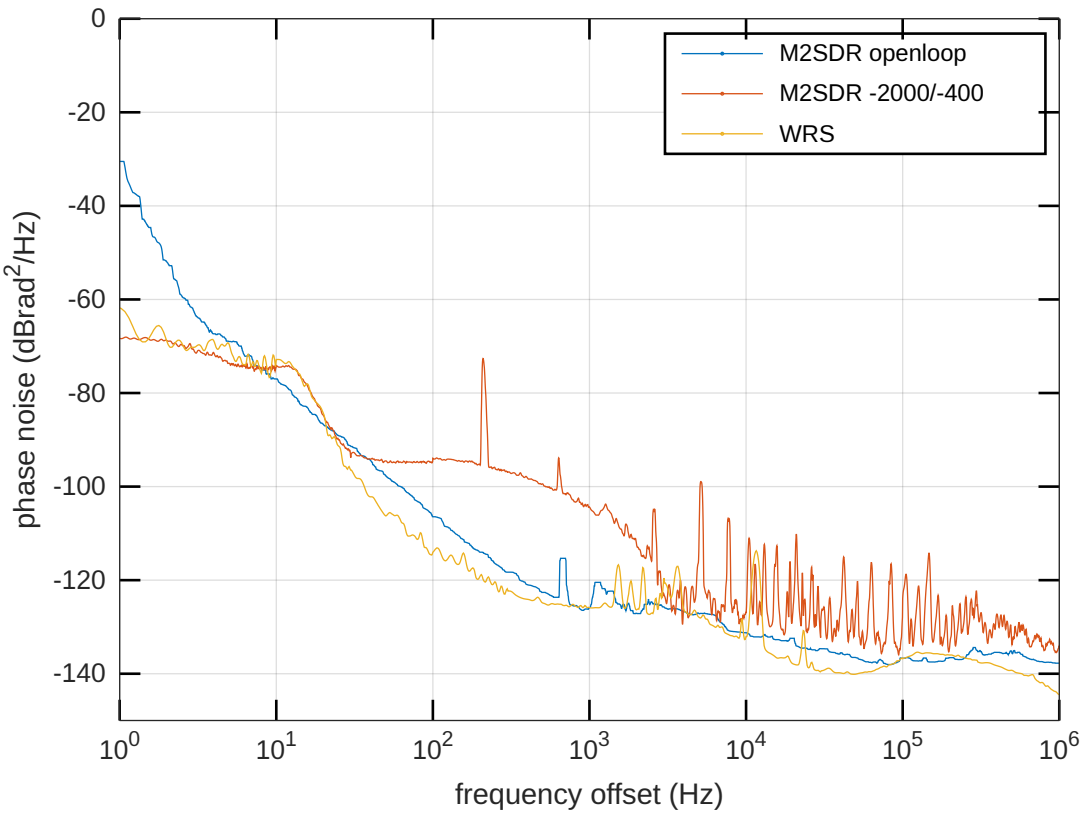
[picture p102: page 1]

M2SDR openloop M2SDR -2000/-400

WRS

phase noise (dBrad2/Hz)

frequency offset (Hz)
